kerokero5150/appleII_deadtest_Swicher_Board/Pictures/IMG_8872.jpeg

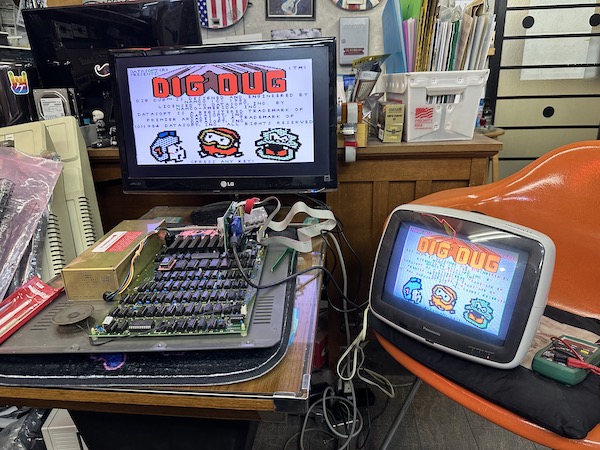
Pictures/IMG_8872.jpeg
